balanceTWK/BalanceDAP/picture/DAPLink_learn1.jpg

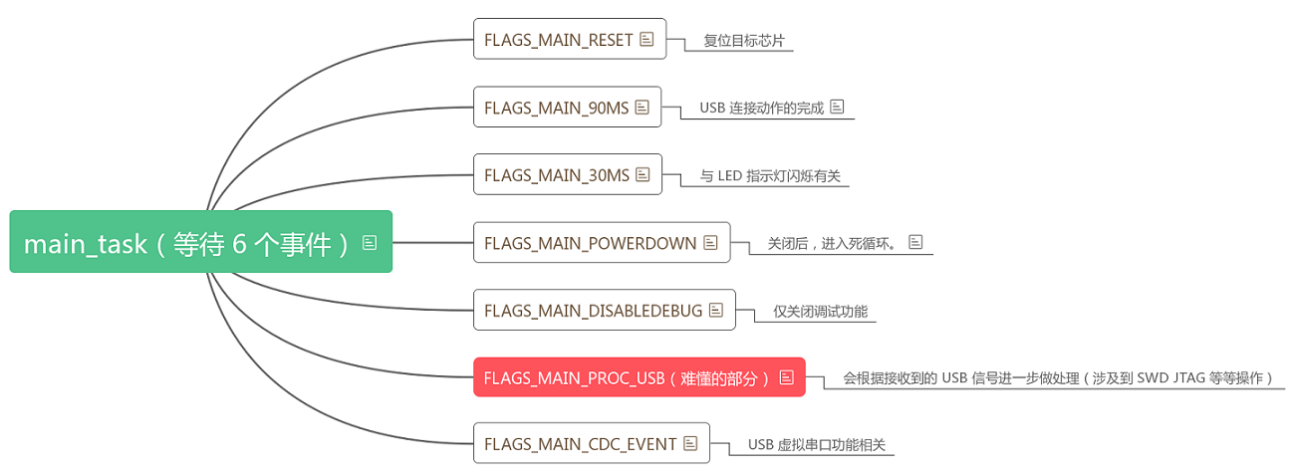
picture/DAPLink_learn1.jpg
