balanceTWK/BalanceDAP/picture/FLAGS_MAIN_PROC_USB.jpg

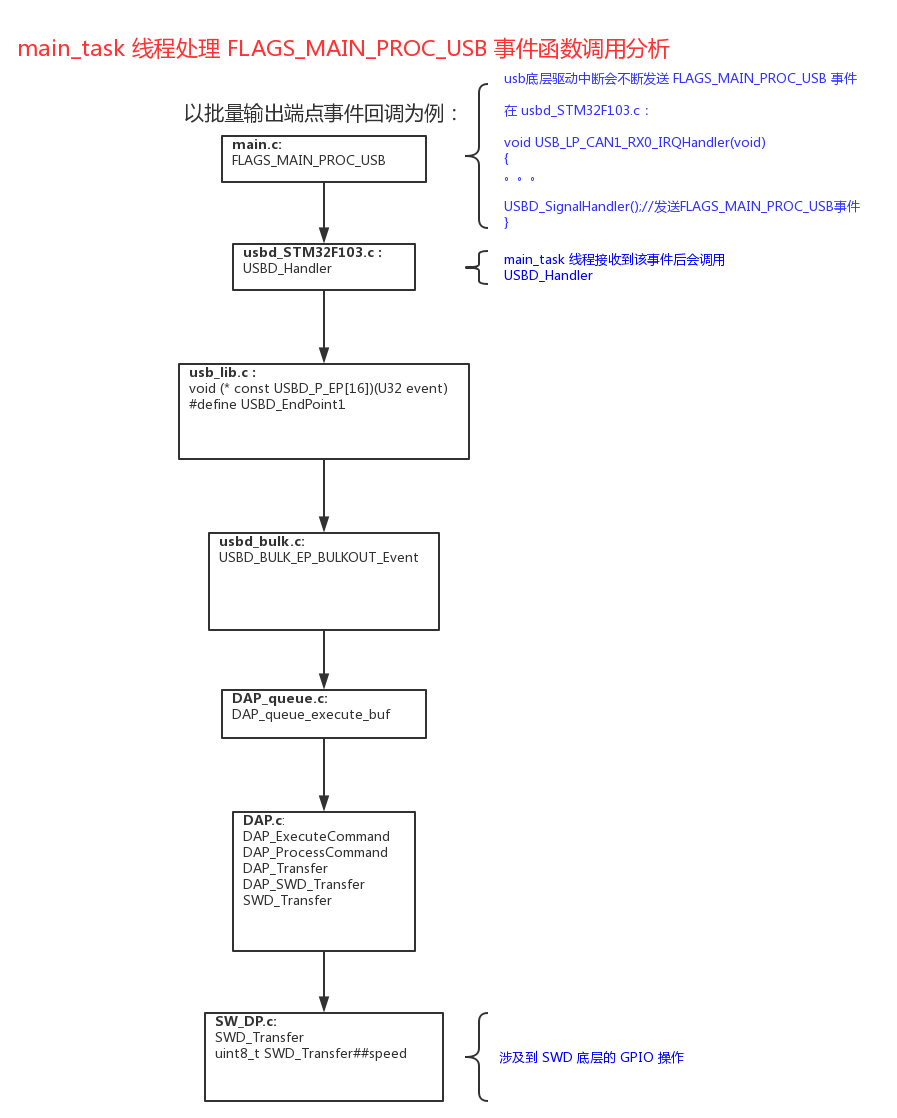
picture/FLAGS_MAIN_PROC_USB.jpg
